makerfx/designer-desks/renders/View3.jpg

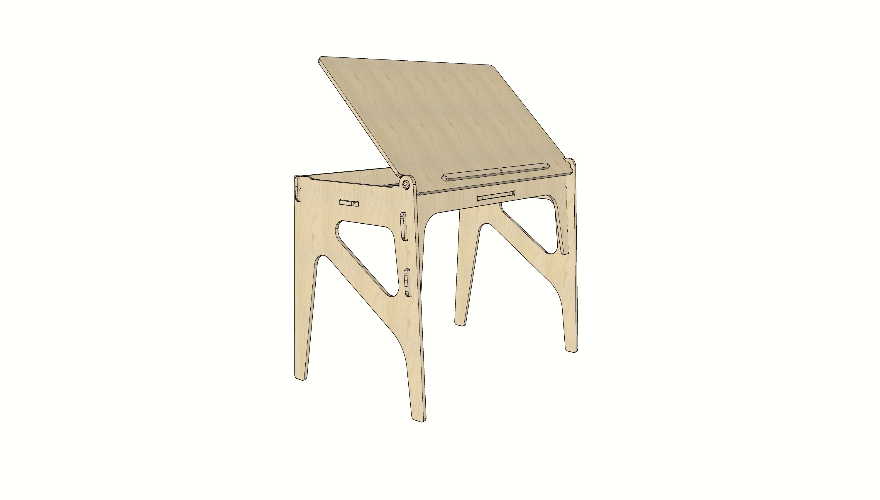
renders/View3.jpg
